bboyho/Motion-Controlled-Wearable-LED-Dance-Harness/Documentation/Arduino_LED_Accelerometer_Calibrating_ADXL335_small.jpg

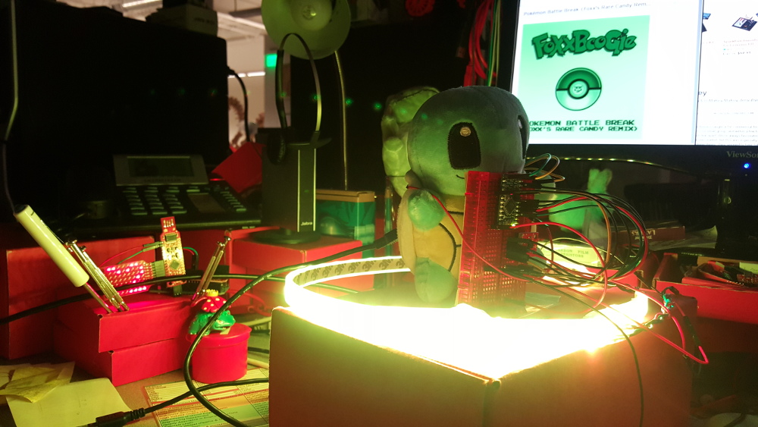
Documentation/Arduino_LED_Accelerometer_Calibrating_ADXL335_small.jpg
